andaniayan-jpg/Tuyyo-Hackclub/cad_assembly/M2.5 Hex Screw v2.step

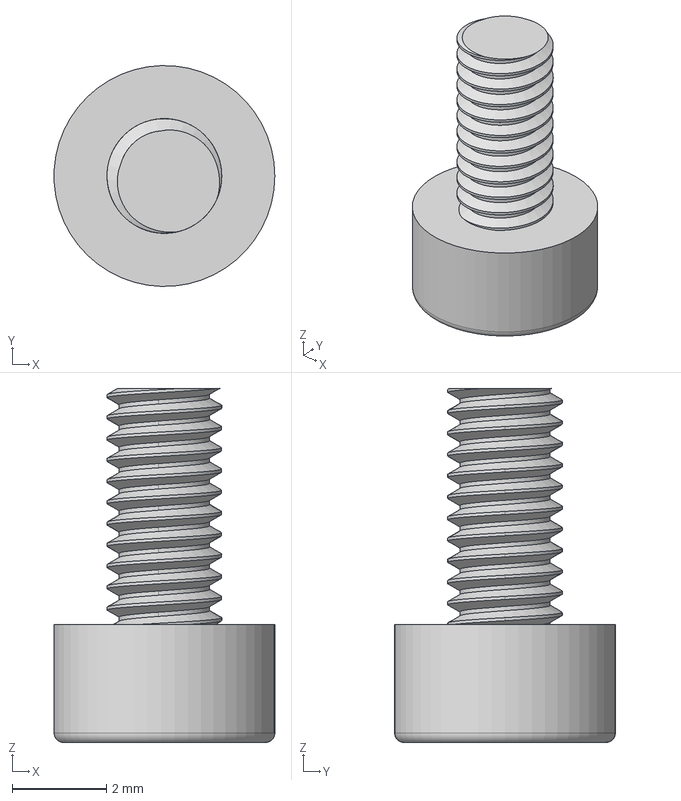
[picture p16: CAD file, 2026-05-07]
cad_assembly/M2.5 Hex Screw v2.step
4.68 x 4.68 x 7.50 mm
